eshazen/ninjanirs-imu/Case/circle.dxf

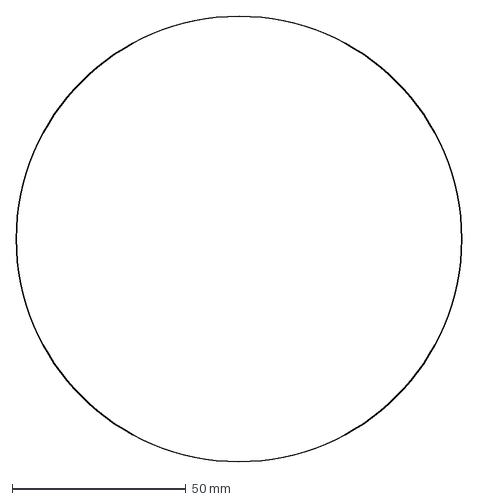
[picture p25: CAD file, 2024-11-25]
Case/circle.dxf
128.1 x 128.1 mm
