eshazen/ninjanirs-imu/KiCAD/imu-board/models/ISM330DHCX.step

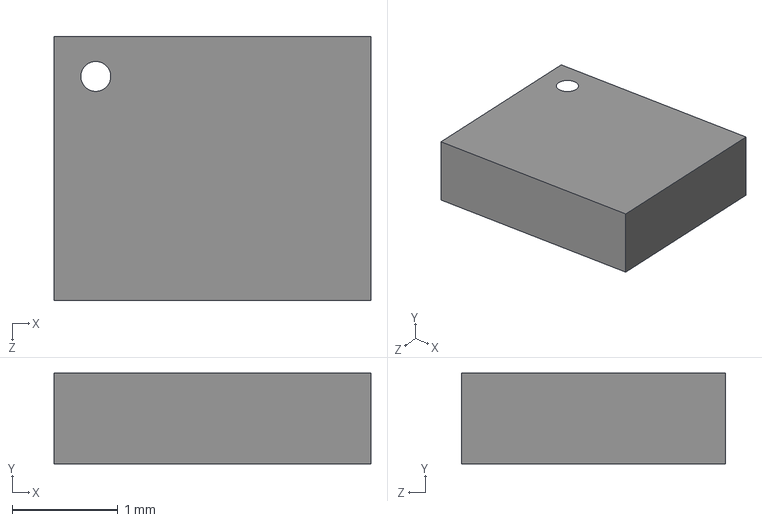
[picture p26: CAD file, 2024-01-10]
KiCAD/imu-board/models/ISM330DHCX.step
3.00 x 0.86 x 2.50 mm
