eshazen/ninjanirs-imu/KiCAD/imu-splitter/3D/1551TGY.stp

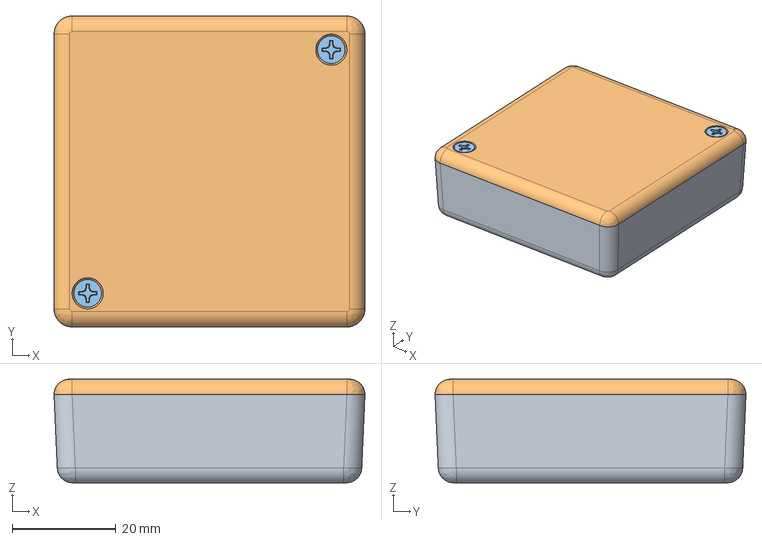
[picture p27: CAD file, 2024-05-08]
KiCAD/imu-splitter/3D/1551TGY.stp
60.0 x 60.0 x 20.0 mm
1551T Box
1551T Lid
