eshazen/ninjanirs-imu/Case/hammond_wall_outer.dxf

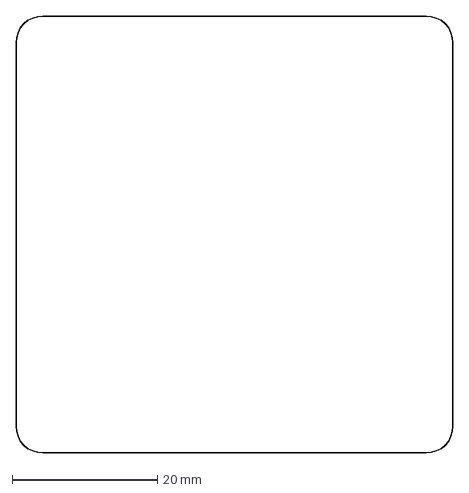
[picture p28: CAD file, 2024-11-25]
Case/hammond_wall_outer.dxf
60.1 x 60.1 mm
