eshazen/ninjanirs-imu/KiCAD/imu-splitter/3D/A-2004-3-4-Group.step

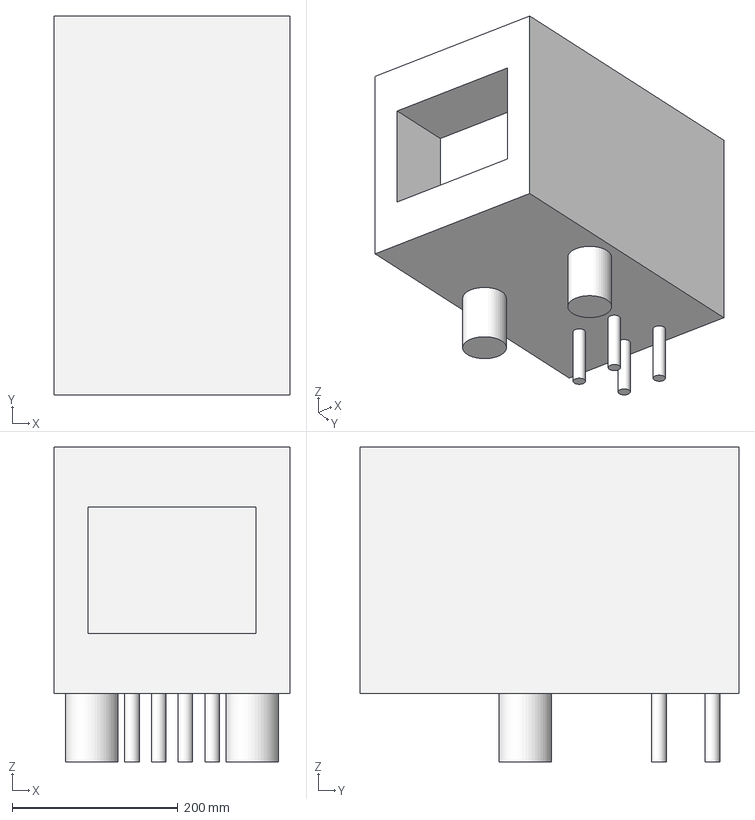
[picture p29: CAD file, 2024-01-11]
KiCAD/imu-splitter/3D/A-2004-3-4-Group.step
284.5 x 457.2 x 379.7 mm
