eshazen/ninjanirs-imu/Case/case_print.stl

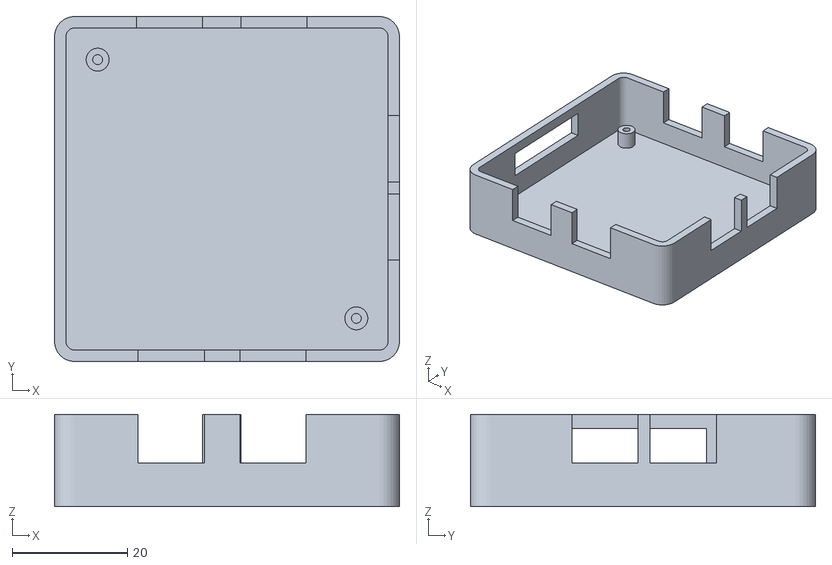
[picture p30: CAD file, 2024-11-25]
Case/case_print.stl
60.0 x 60.0 x 16.0
