eshazen/ninjanirs-imu/KiCAD/imu-splitter/3D/1551T.dxf

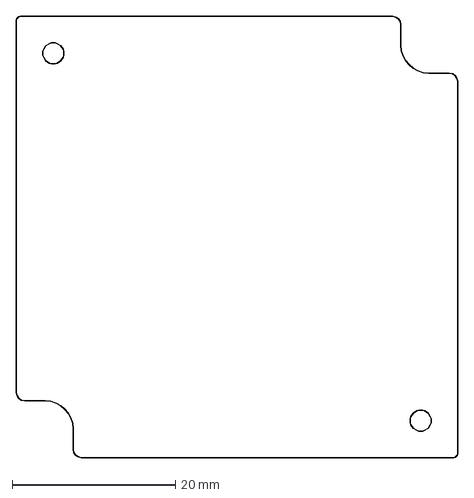
[picture p31: CAD file, 2024-01-11]
KiCAD/imu-splitter/3D/1551T.dxf
54.0 x 54.0 mm
