eshazen/ninjanirs-imu/Case/hammond_wall_inner.dxf

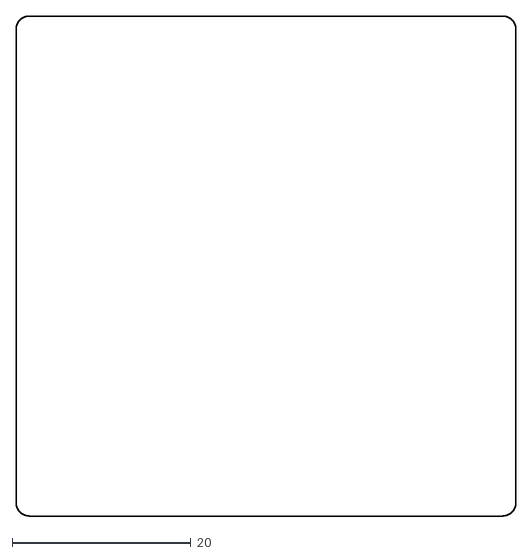
[picture p32: CAD file, 2024-11-25]
Case/hammond_wall_inner.dxf
56.0 x 56.0
