eshazen/ninjanirs-imu/Case/case_print2.stl

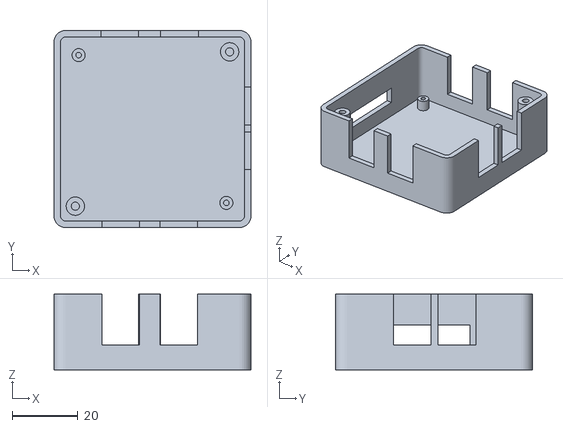
[picture p33: CAD file, 2024-11-25]
Case/case_print2.stl
60.0 x 60.0 x 23.0
