eshazen/ninjanirs-imu/Case/hammond_wall_xs.dxf

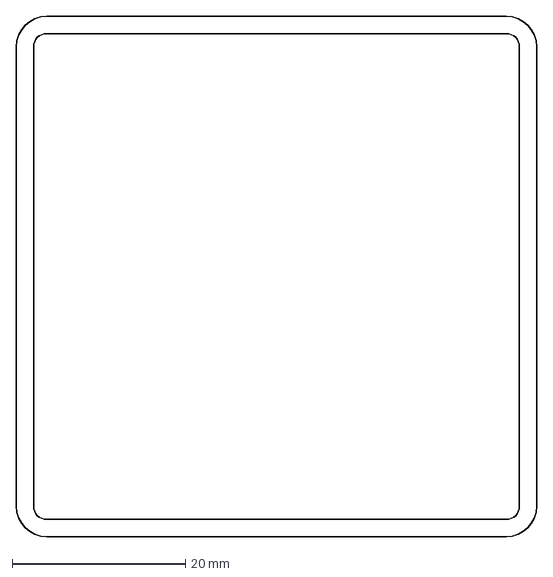
[picture p34: CAD file, 2024-11-25]
Case/hammond_wall_xs.dxf
60.0 x 60.0 mm
