eshazen/ninjanirs-imu/Software/avr-imu-gpio-test/sample_imu_data_1.ods

Temp | XG | YG | ZG | XA | YA | ZA | X UP | X DN | Y UP | Y DN | Z UP | Z DN
-846 | -70 | -41 | -37 | -1855 | -107 | 8105 | 0 | 0 | 0 | 0 | 1 | 0
-850 | -69 | -43 | -37 | -1854 | -106 | 8105 | 0 | 0 | 0 | 0 | 1 | 0
-848 | -71 | -41 | -39 | -1855 | -107 | 8107 | 0 | 0 | 0 | 0 | 1 | 0
-858 | -72 | -42 | -39 | -1853 | -106 | 8108 | 0 | 0 | 0 | 0 | 1 | 0
-858 | -67 | -47 | -38 | -1851 | -106 | 8106 | 0 | 0 | 0 | 0 | 1 | 0
-858 | -72 | -42 | -40 | -1856 | -107 | 8108 | 0 | 0 | 0 | 0 | 1 | 0
-860 | -72 | -45 | -40 | -1850 | -108 | 8108 | 0 | 0 | 0 | 0 | 1 | 0
-868 | -71 | -43 | -40 | -1853 | -107 | 8104 | 0 | 0 | 0 | 0 | 1 | 0
-858 | -72 | -40 | -39 | -1852 | -105 | 8107 | 0 | 0 | 0 | 0 | 1 | 0
-860 | -68 | -42 | -38 | -1854 | -108 | 8106 | 0 | 0 | 0 | 0 | 1 | 0
-868 | -1435 | -7237 | -1196 | 613 | 211 | 8162 | 0 | 0 | 0 | 0 | 1 | 0
-870 | -4349 | -1020 | 178 | 105 | 824 | 7872 | 0 | 0 | 0 | 0 | 1 | 0
-876 | -1043 | 597 | 129 | -176 | -148 | 8173 | 0 | 0 | 0 | 0 | 1 | 0
-870 | 517 | 793 | -119 | -416 | -605 | 8384 | 0 | 0 | 0 | 0 | 1 | 0
-858 | -4940 | 18966 | -528 | -4164 | -979 | 7567 | 0 | 0 | 0 | 0 | 1 | 0
-856 | -3849 | 9028 | 1207 | -4714 | -165 | -6974 | 0 | 0 | 0 | 0 | 0 | 0
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
